Selanarix/DepthSensor/pictures/IMG_0990.JPG

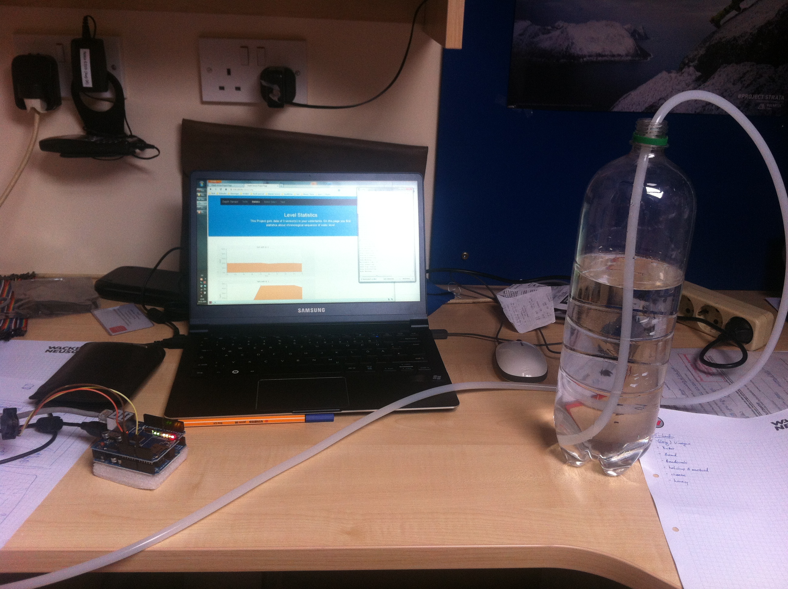
pictures/IMG_0990.JPG
