Selanarix/DepthSensor/pictures/IMG_0991.JPG

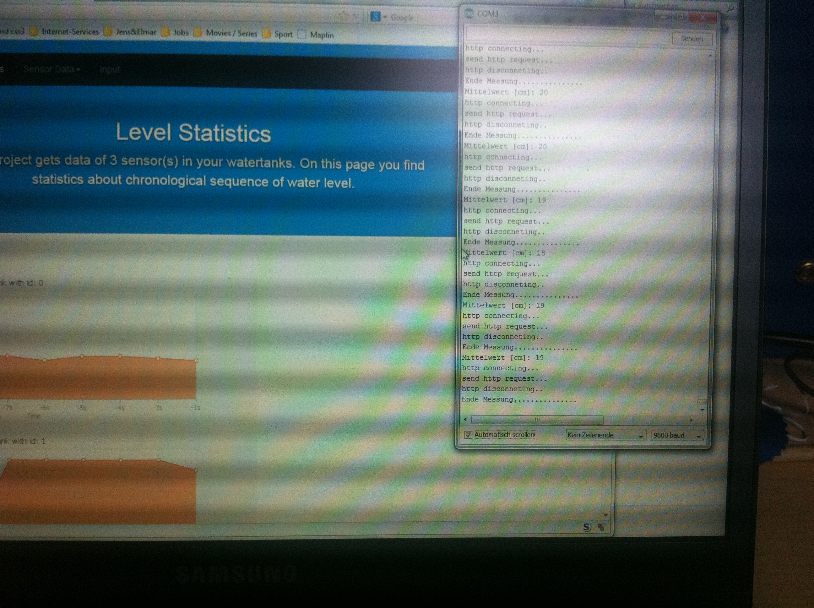
pictures/IMG_0991.JPG
