Selanarix/DepthSensor/pictures/IMG_0992.JPG

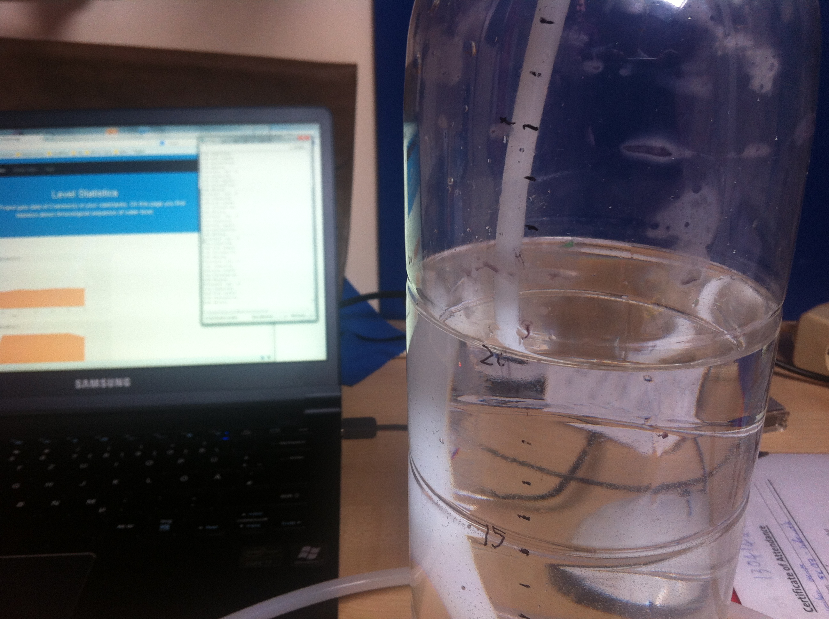
pictures/IMG_0992.JPG
