Selanarix/DepthSensor/pictures/IMG_0993.JPG

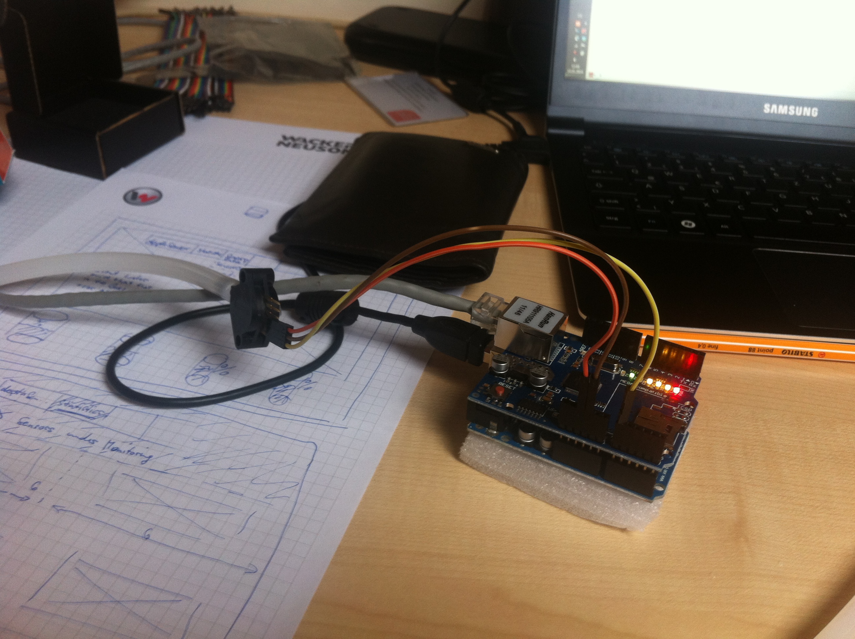
pictures/IMG_0993.JPG
