Selanarix/DepthSensor/pictures/MPX2100DP oszi/IMG_20140116_185109.jpg

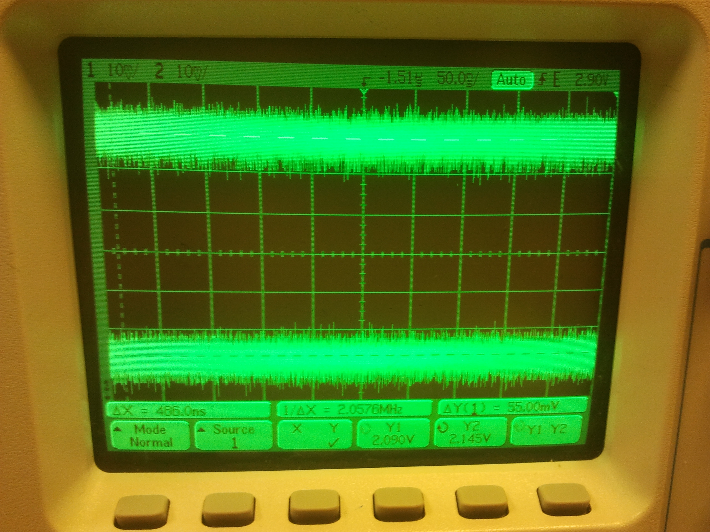
pictures/MPX2100DP oszi/IMG_20140116_185109.jpg
